rpolubinskii/diffbot-ros2/ros2_ws/bringup/config/ekf.yaml

ekf_filter_node:
  ros__parameters:
    frequency: 15.0
    sensor_timeout: 0.2
    two_d_mode: true
    publish_tf: true
    map_frame: map
    odom_frame: odom
    base_link_frame: base_footprint
    world_frame: odom
    transform_time_offset: 0.0
    transform_timeout: 0.0
    print_diagnostics: true
    predict_to_current_time: true

    odom0: /diffbot_base_controller/odom
    odom0_config: [false, false, false,
                   false, false, false,
                   true, true, false,
                   false, false, false,
                   false, false, false]
    odom0_differential: false
    odom0_relative: false
    odom0_queue_size: 10

    odom1: /rtabmap/icp_odom_reweighted
    odom1_config: [false, false, false,
                   false, false, true,
                   true, false, false,
                   false, false, true,
                   false, false, false]
    odom1_differential: false
    odom1_relative: false
    odom1_queue_size: 10

    imu0: /imu/data_body
    imu0_config: [false, false, false,
                  false, false, false,
                  false, false, false,
                  false, false, true,
                  false, false, false]
    imu0_differential: false
    imu0_relative: false
    imu0_queue_size: 20
    imu0_remove_gravitational_acceleration: false
